ImogenWren/glowworm-micro/circuit-modelling/battery-level-circuit.asc

R1: res; 100k
R2: res; 330k
R4: res; 100k
R5: res; 220k
U1: UniversalOpAmp2
V6: voltage; 3.3
V7: voltage; 4.2
Named nets: 0, Vsupply, Vbatt, SCALED_VOLTAGE
;.tran 0 0.1 0 1
.dc V7 3.2 4.2 0.01
