ImogenWren/glowworm-micro/glowworm-firmware/batteryMonitor.h

calibration::cal_data cal_map[10] = {
  { 2.72, 3.238 },
  { 2.74, 3.346}, 
  { 2.76, 3.444},
  { 2.77, 3.535 },
  { 2.79, 3.624 },
  { 2.80, 3.717 },
  { 2.82, 3.827 },
  { 2.84, 3.976 },
  { 2.86, 4.105 },
  { 2.87, 4.254 }
};

calibration::cal_data cal_map_2[10] = {    // merge conflict will need to retest on new hardware anyway
  { 1.68, 2.965 },
  { 1.87, 3.161 },
  { 2.08, 3.358 },
  { 2.39, 3.672 },
  { 2.47, 3.819 },
  { 2.70, 3.978 },
  { 2.885, 4.000 },
  { 2.90, 4.022 },
  { 2.92, 4.056 },
  { 3.04, 4.324 }
  
  };

// Battery level goes from 0 to above 3
// now with averaging to stop the animation jumping up and down all the time
#define NUM_SAMPLES 100

int sampleIndex = 0;
int sampleVal = 0;
int sampleSum = 0;
int sampleRead[NUM_SAMPLES];
float averaged = 0;


void batteryMonitor() {
  uint8_t temp_batt_level = 0;


  sampleSum = sampleSum - sampleRead[sampleIndex];  // remove the oldest sample from the sum
  sampleVal = analogRead(BATTERY_SENSE_PIN);
  sampleRead[sampleIndex] = sampleVal;
  sampleSum = sampleSum + sampleVal;
  sampleIndex = (sampleIndex + 1) % NUM_SAMPLES;

  averaged = float(sampleSum) / float(NUM_SAMPLES);

  float battery_adc = averaged;
  float measured_voltage = battery_adc * 3.1E-3;  //current value found via measurement  //22265625
  Serial.print("adc: ");
  Serial.print(averaged);
  Serial.print("  measuredV: ");
  Serial.print(measured_voltage);
  batteryVoltage = cal.do_table_calibration(measured_voltage, cal_map);
  if (batteryVoltage <= 3.35) temp_batt_level = 0;
  else if (batteryVoltage > 3.37 && batteryVoltage <= 3.75) temp_batt_level = 1;
  else if (batteryVoltage > 3.75 && batteryVoltage <= 4.0) temp_batt_level = 2;
  else if (batteryVoltage > 4.0 && batteryVoltage <= 4.14) temp_batt_level = 3;
  else if (batteryVoltage > 4.14) temp_batt_level = 4;



  if (battery_samples_taken < BATTERY_SAMPLES_REQ) {
    batt_indicator_unsmoothed[battery_samples_taken] = temp_batt_level;
    battery_samples_taken++;
  } else if (battery_samples_taken >= BATTERY_SAMPLES_REQ) {
    battery_indicator_level = 0;
    for (int i = 0; i < battery_samples_taken; i++) {
      battery_indicator_level += batt_indicator_unsmoothed[i];
    }
    battery_indicator_level = battery_indicator_level / battery_samples_taken;
    battery_samples_taken = 0;
  }

  Serial.print(" Vbat: ");
  Serial.print(batteryVoltage);
  Serial.print(" Indicator: ");
  Serial.println(battery_indicator_level);
}
